donaldsonlab/PPT-Chamber/Main/Dividers/Climbing Wall Drawings/Two_Thirds_climbing_ladder.DXF

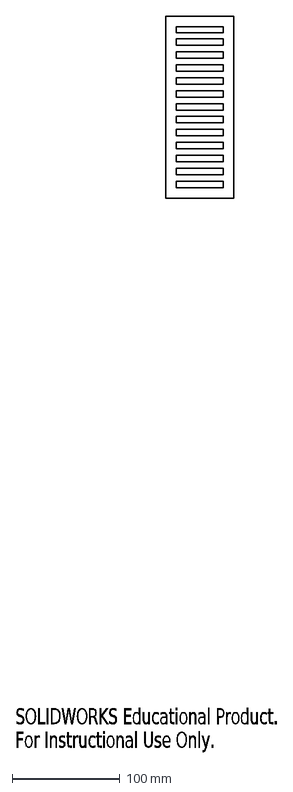
[picture p16: CAD file, 2024-10-31]
Main/Dividers/Climbing Wall Drawings/Two_Thirds_climbing_ladder.DXF
SOLIDWORKS Educational Product.
For Instructional Use Only.
