donaldsonlab/PPT-Chamber/Main/PPT_SideWall.SLDPRT

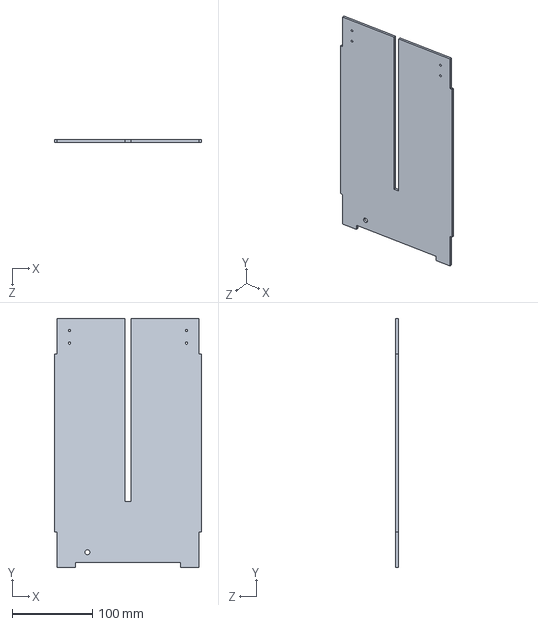
[picture p17: CAD file, 2024-09-06]
Main/PPT_SideWall.SLDPRT
184.1 x 311.1 x 3.17 mm
