donaldsonlab/PPT-Chamber/STL/PPT_cornerBrace_oppo.STL

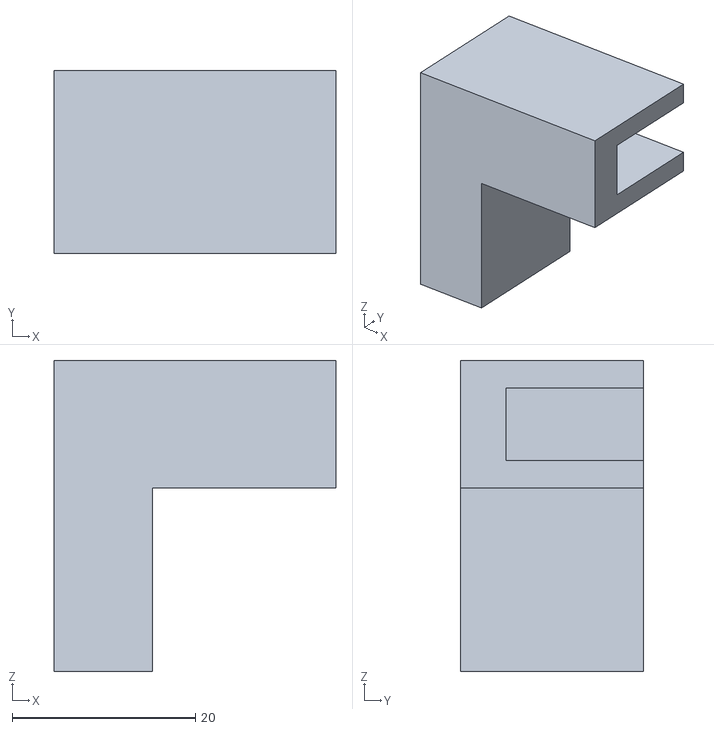
[picture p18: CAD file, 2022-10-21]
STL/PPT_cornerBrace_oppo.STL
30.8 x 20.0 x 33.9
