donaldsonlab/PPT-Chamber/2-Chamber/PPT2_Base.SLDPRT

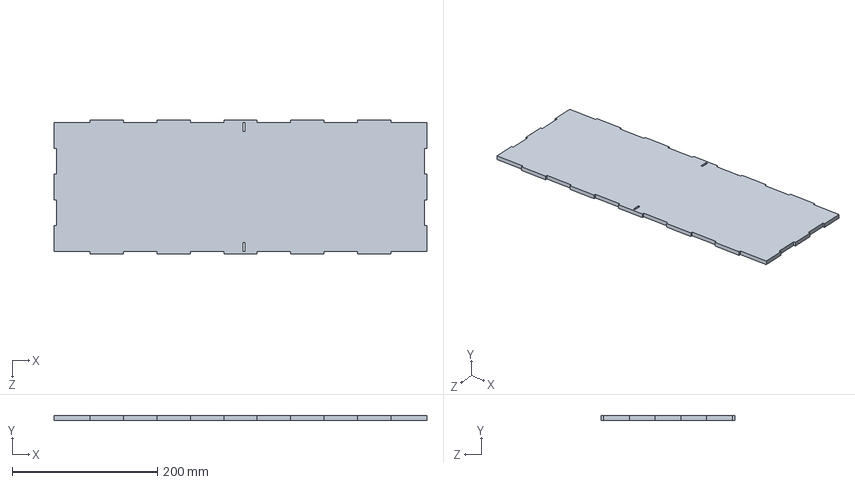
[picture p19: CAD file, 2023-02-03]
2-Chamber/PPT2_Base.SLDPRT
514.3 x 6.35 x 184.2 mm
