donaldsonlab/PPT-Chamber/2-Chamber/printing/slot_cover.DXF

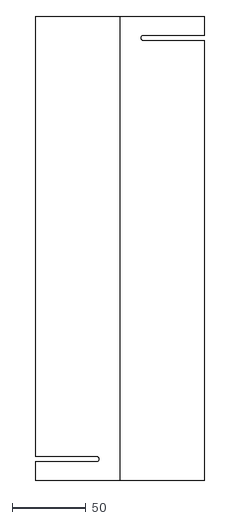
[picture p20: CAD file, 2023-02-03]
2-Chamber/printing/slot_cover.DXF
115.3 x 315.0
