donaldsonlab/PPT-Chamber/Laser Cutting/PPT_Insert_cut.DXF

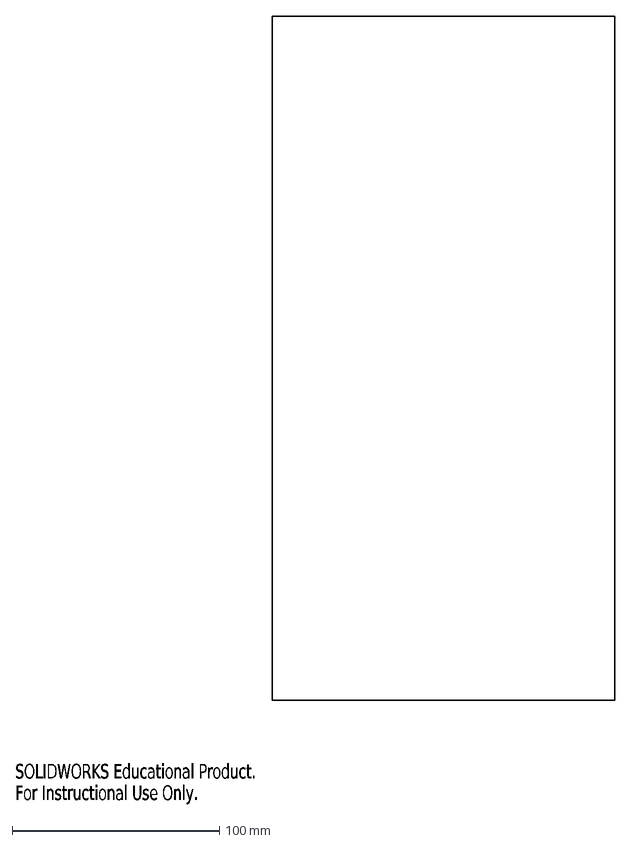
[picture p21: CAD file, 2022-07-01]
Laser Cutting/PPT_Insert_cut.DXF
SOLIDWORKS Educational Product.
For Instructional Use Only.
