donaldsonlab/PPT-Chamber/Main - 2 Chamber PPT/Cutting/PPT_InsertGuide_Large.DXF

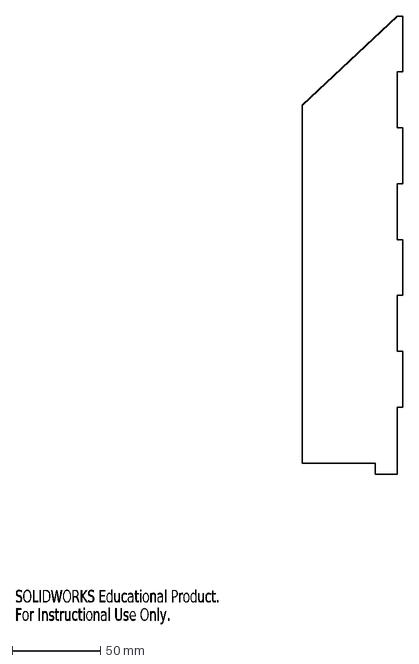
[picture p22: CAD file, 2023-08-11]
Main - 2 Chamber PPT/Cutting/PPT_InsertGuide_Large.DXF
SOLIDWORKS Educational Product.
For Instructional Use Only.
