donaldsonlab/PPT-Chamber/Main - 2 Chamber PPT/drawing files 20231101/PPT_Box_Nest.DXF

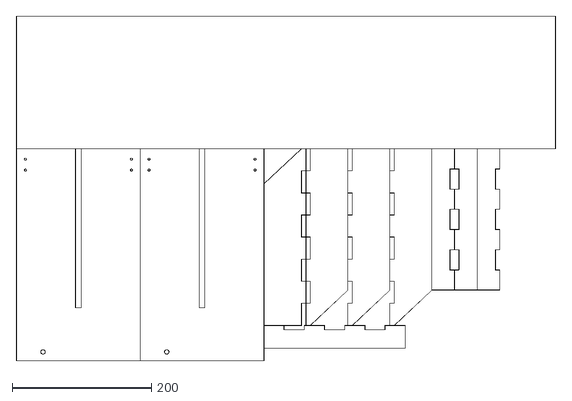
[picture p23: CAD file, 2024-09-06]
Main - 2 Chamber PPT/drawing files 20231101/PPT_Box_Nest.DXF
775.1 x 495.7
