donaldsonlab/PPT-Chamber/Main - 2 Chamber PPT/Drawings/PPT_InsertGuide_Small_longer.DXF

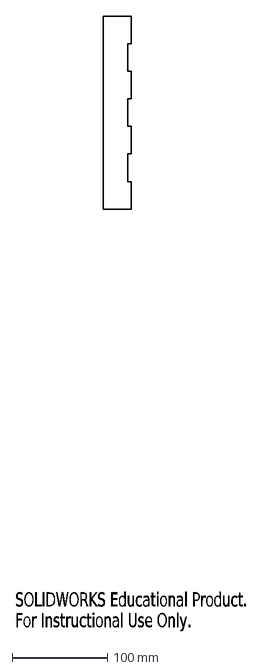
[picture p24: CAD file, 2023-08-11]
Main - 2 Chamber PPT/Drawings/PPT_InsertGuide_Small_longer.DXF
SOLIDWORKS Educational Product.
For Instructional Use Only.
