donaldsonlab/PPT-Chamber/Main/Dividers/perforated_divider.SLDPRT

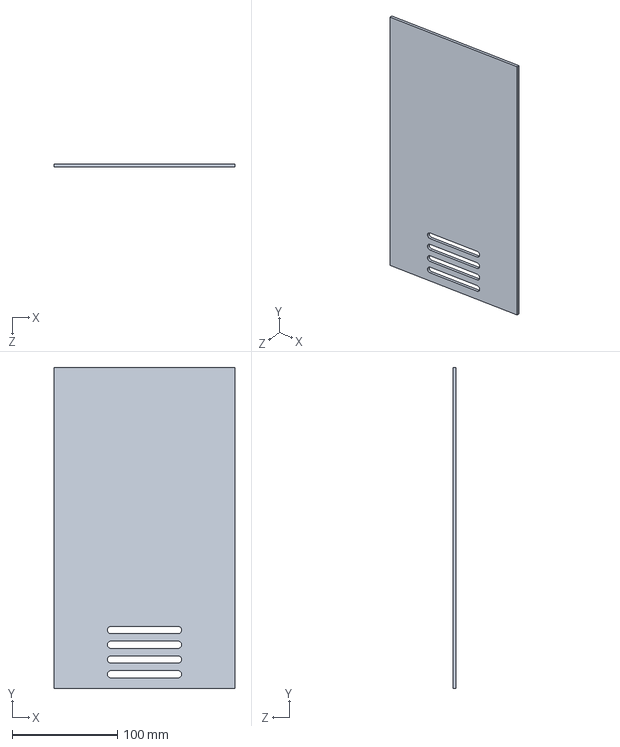
[picture p25: CAD file, 2024-10-31]
Main/Dividers/perforated_divider.SLDPRT
171.4 x 304.8 x 3.17 mm
