donaldsonlab/PPT-Chamber/Main/PPT_LongWall.SLDPRT

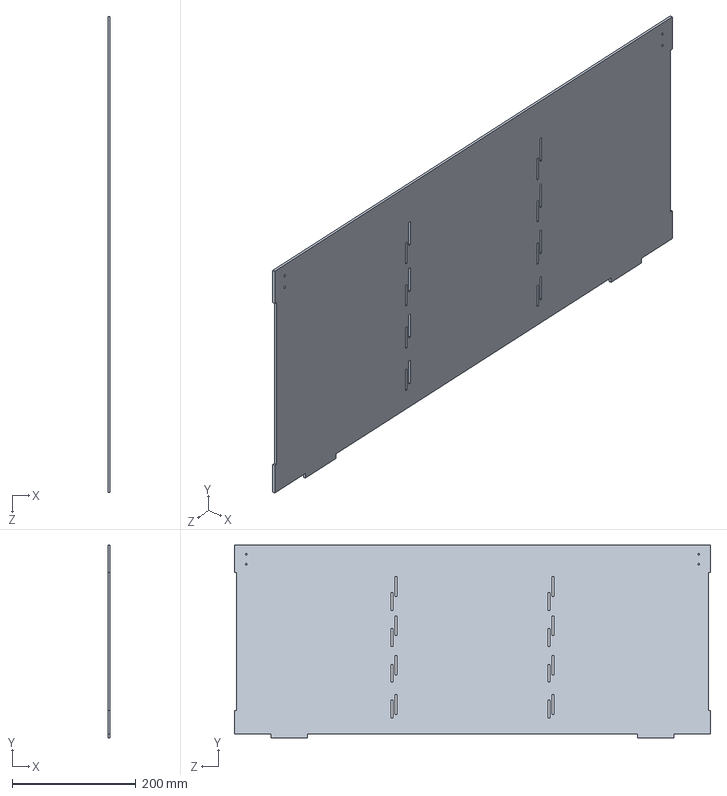
[picture p26: CAD file, 2024-09-06]
Main/PPT_LongWall.SLDPRT
3.17 x 311.1 x 768.3 mm
