donaldsonlab/PPT-Chamber/2-Chamber/PPT2_holeCover.SLDPRT

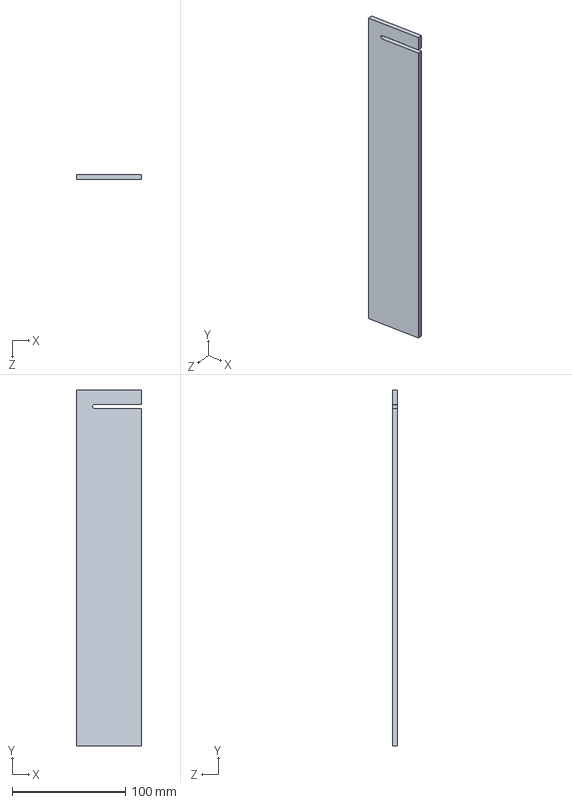
[picture p27: CAD file, 2023-02-03]
2-Chamber/PPT2_holeCover.SLDPRT
57.5 x 314.7 x 4.76 mm
