donaldsonlab/PPT-Chamber/2-Chamber/printing/eigth_inch.DXF

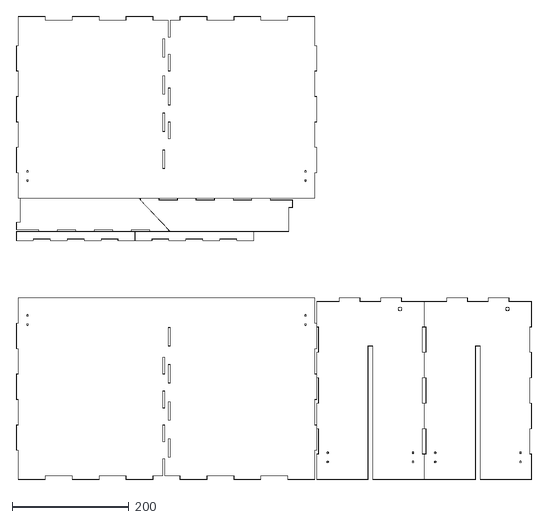
[picture p28: CAD file, 2023-02-03]
2-Chamber/printing/eigth_inch.DXF
883.0 x 793.5
