donaldsonlab/PPT-Chamber/Laser Cutting/PPT_holeCover.DXF

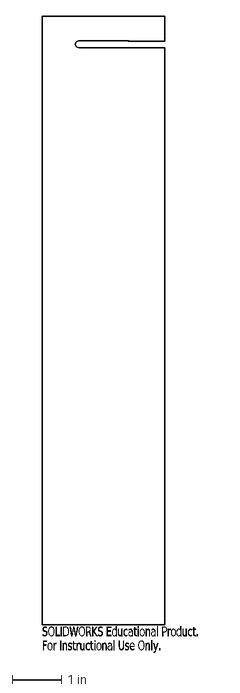
[picture p29: CAD file, 2022-02-18]
Laser Cutting/PPT_holeCover.DXF
SOLIDWORKS Educational Product.
For Instructional Use Only.
