donaldsonlab/PPT-Chamber/Main - 2 Chamber PPT/Cutting/PPT_Insert.DXF

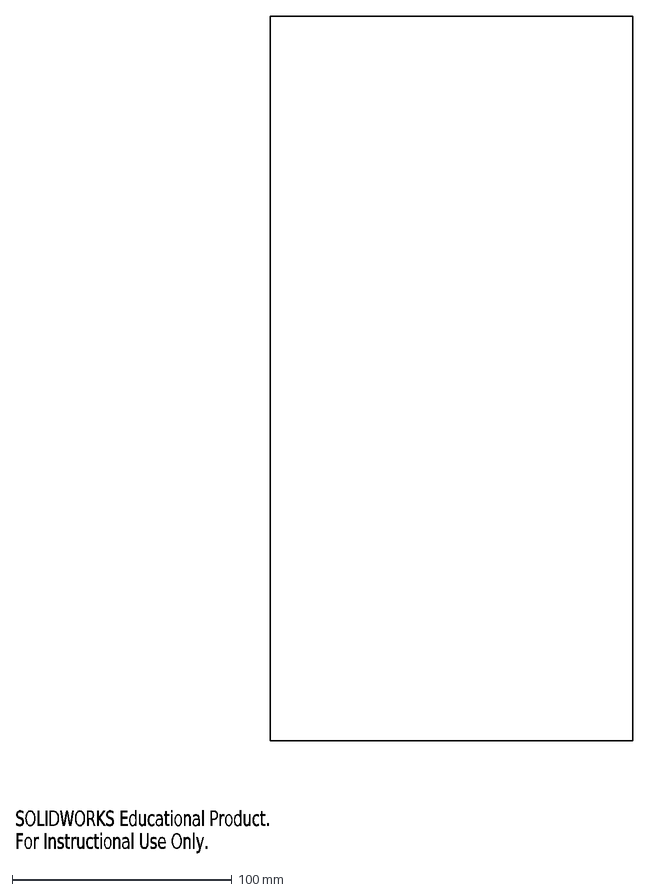
[picture p30: CAD file, 2023-08-11]
Main - 2 Chamber PPT/Cutting/PPT_Insert.DXF
SOLIDWORKS Educational Product.
For Instructional Use Only.
