donaldsonlab/PPT-Chamber/Main - 2 Chamber PPT/drawing files 20231101/PPT_SideWall.DXF

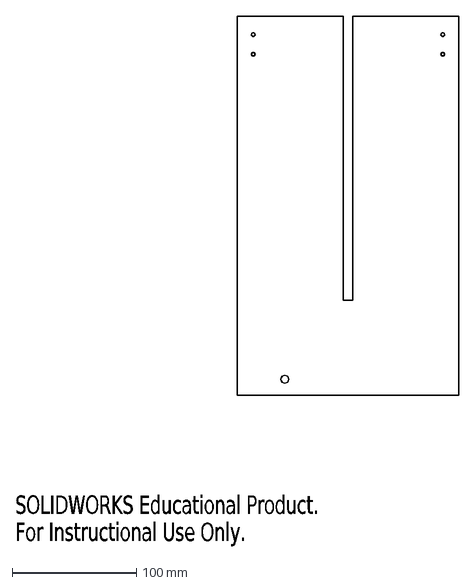
[picture p31: CAD file, 2024-09-06]
Main - 2 Chamber PPT/drawing files 20231101/PPT_SideWall.DXF
SOLIDWORKS Educational Product.
For Instructional Use Only.
