donaldsonlab/PPT-Chamber/Main/Dividers/Climbing Wall Drawings/One_Third_climbing_spacer.DXF

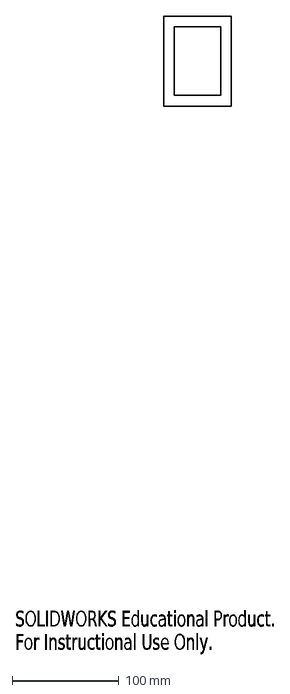
[picture p32: CAD file, 2024-10-31]
Main/Dividers/Climbing Wall Drawings/One_Third_climbing_spacer.DXF
SOLIDWORKS Educational Product.
For Instructional Use Only.
