donaldsonlab/PPT-Chamber/STL/PPT_cornerBracket.STL

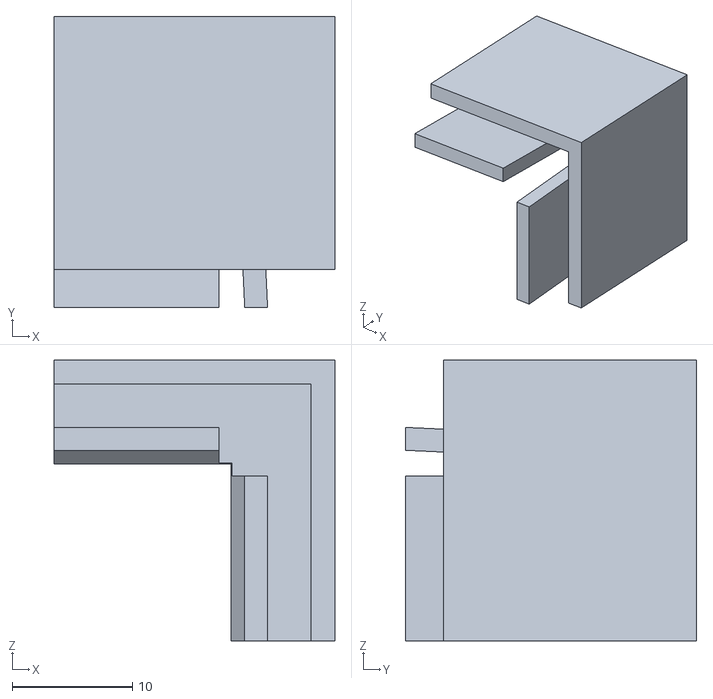
[picture p33: CAD file, 2022-02-18]
STL/PPT_cornerBracket.STL
23.4 x 24.2 x 23.4
