donaldsonlab/PPT-Chamber/Laser Cutting/lasercut1.dxf

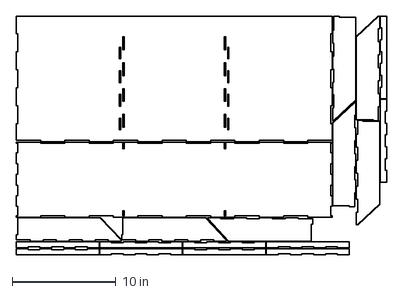
[picture p34: CAD file, 2022-02-18]
Laser Cutting/lasercut1.dxf
35.8 x 23.1 in
