donaldsonlab/PPT-Chamber/Main - 2 Chamber PPT/Cutting/PPT_Floor.DXF

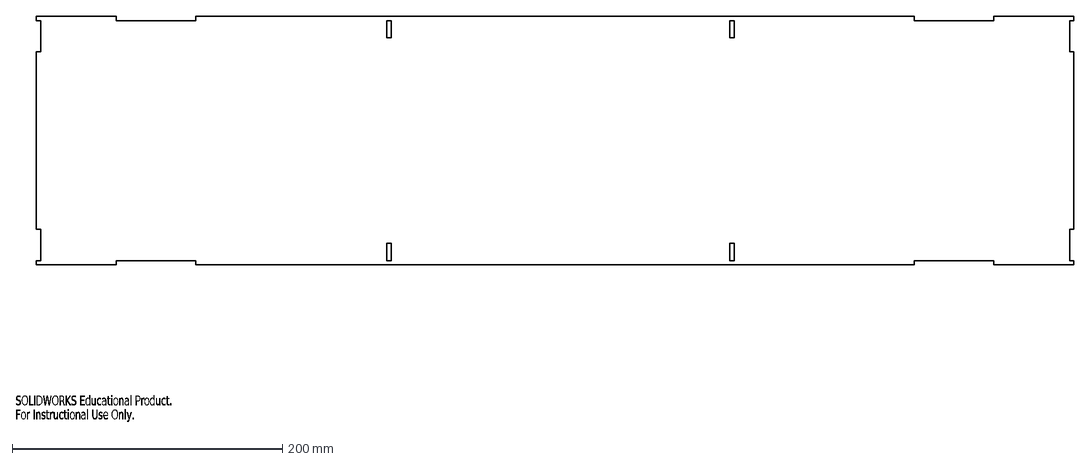
[picture p35: CAD file, 2023-08-11]
Main - 2 Chamber PPT/Cutting/PPT_Floor.DXF
SOLIDWORKS Educational Product.
For Instructional Use Only.
