donaldsonlab/PPT-Chamber/Main - 2 Chamber PPT/drawing files 20231101/PPT_InsertGuide_Large.DXF

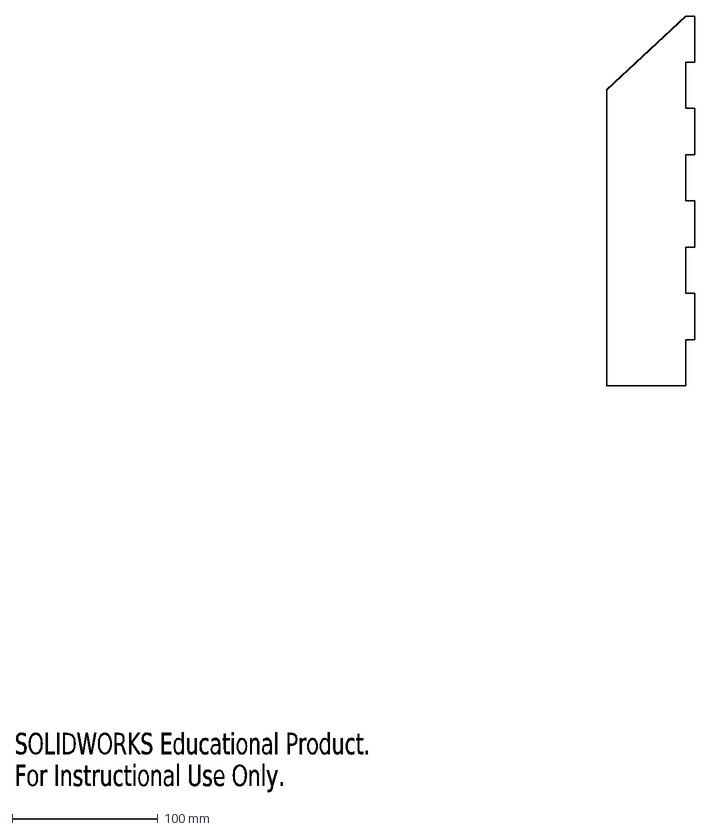
[picture p36: CAD file, 2024-09-06]
Main - 2 Chamber PPT/drawing files 20231101/PPT_InsertGuide_Large.DXF
SOLIDWORKS Educational Product.
For Instructional Use Only.
