donaldsonlab/PPT-Chamber/Main - 2 Chamber PPT/DXF Files 20231108/PPT_SideWall.DXF

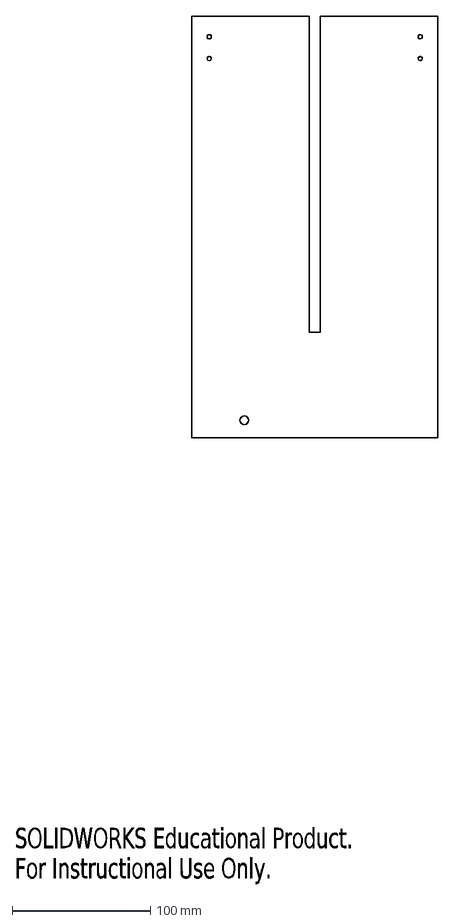
[picture p37: CAD file, 2024-09-06]
Main - 2 Chamber PPT/DXF Files 20231108/PPT_SideWall.DXF
SOLIDWORKS Educational Product.
For Instructional Use Only.
