donaldsonlab/PPT-Chamber/Main - 2 Chamber PPT/PPT_InsertGuide_Large.SLDPRT

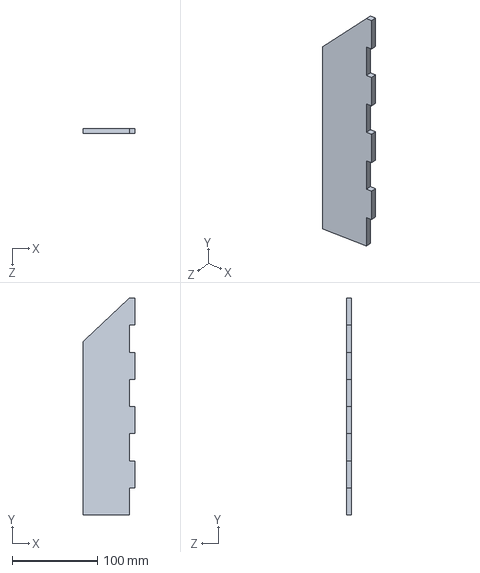
[picture p38: CAD file, 2024-09-06]
Main - 2 Chamber PPT/PPT_InsertGuide_Large.SLDPRT
60.3 x 254.0 x 6.35 mm
