donaldsonlab/PPT-Chamber/Main/Dividers/mesh_divider.SLDPRT

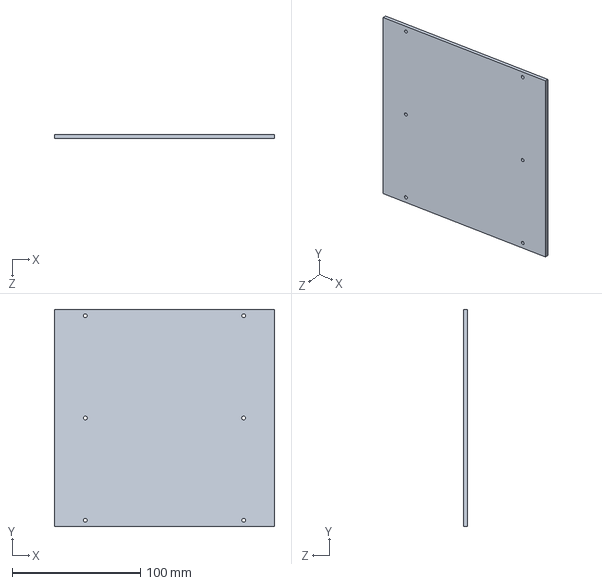
[picture p39: CAD file, 2023-08-11]
Main/Dividers/mesh_divider.SLDPRT
171.4 x 169.3 x 3.17 mm
