donaldsonlab/PPT-Chamber/STL/PPT_miscutPlug.STL

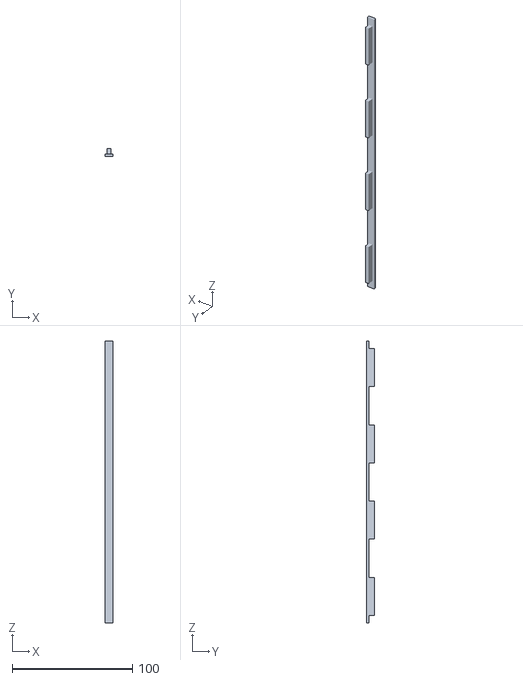
[picture p40: CAD file, 2022-02-18]
STL/PPT_miscutPlug.STL
6.35 x 6.76 x 235.0
