donaldsonlab/PPT-Chamber/2-Chamber/PPT2_Long_Wall.SLDPRT

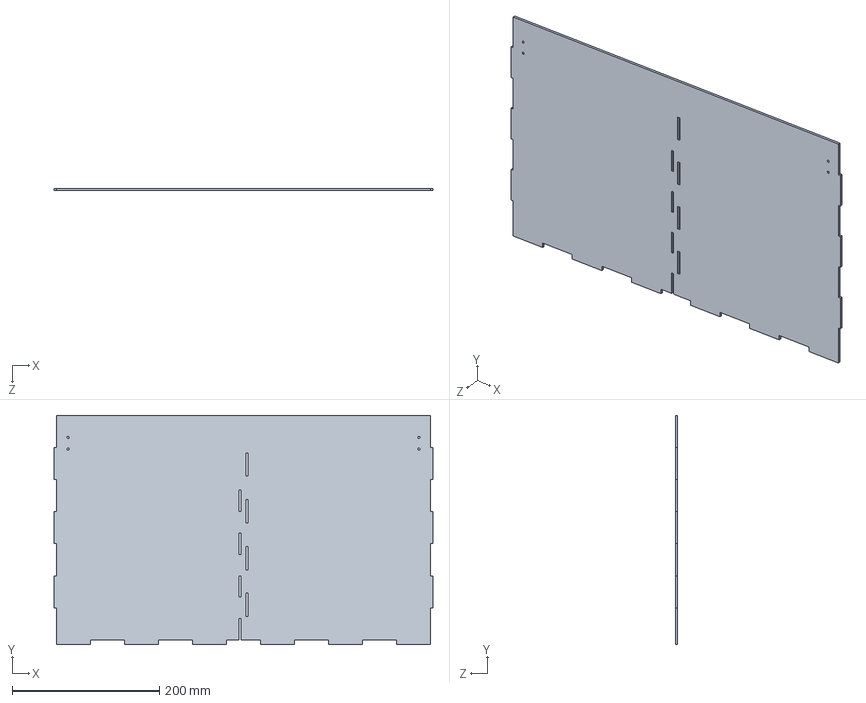
[picture p41: CAD file, 2023-02-03]
2-Chamber/PPT2_Long_Wall.SLDPRT
514.3 x 311.1 x 3.17 mm
