donaldsonlab/PPT-Chamber/Laser Cutting/PPT_Floor.DXF

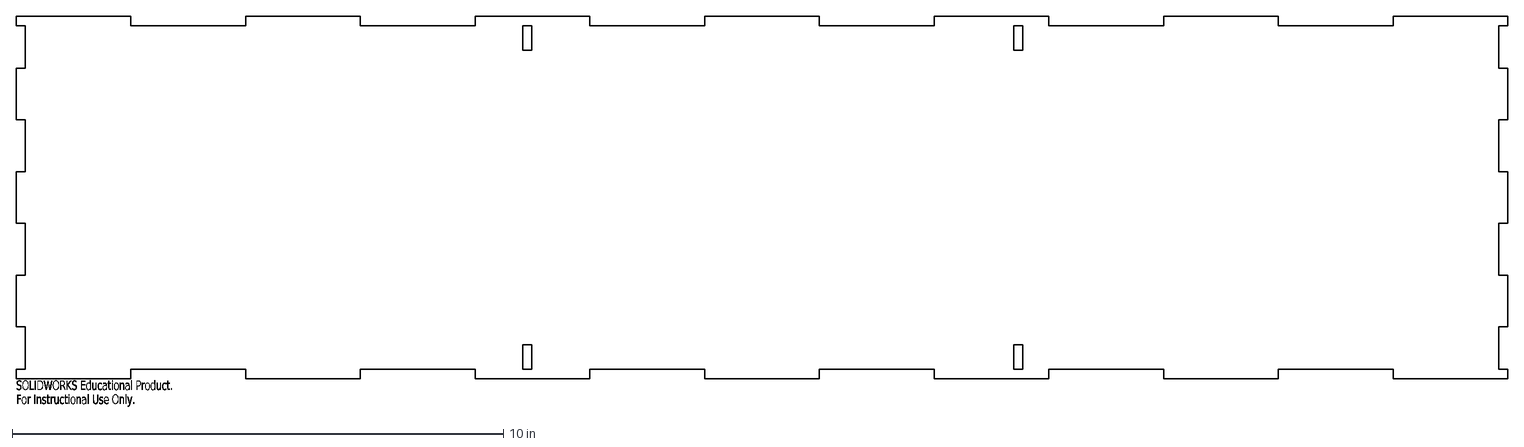
[picture p42: CAD file, 2022-02-18]
Laser Cutting/PPT_Floor.DXF
SOLIDWORKS Educational Product.
For Instructional Use Only.
