donaldsonlab/PPT-Chamber/Main - 2 Chamber PPT/Cutting/PPT_LongWall.DXF

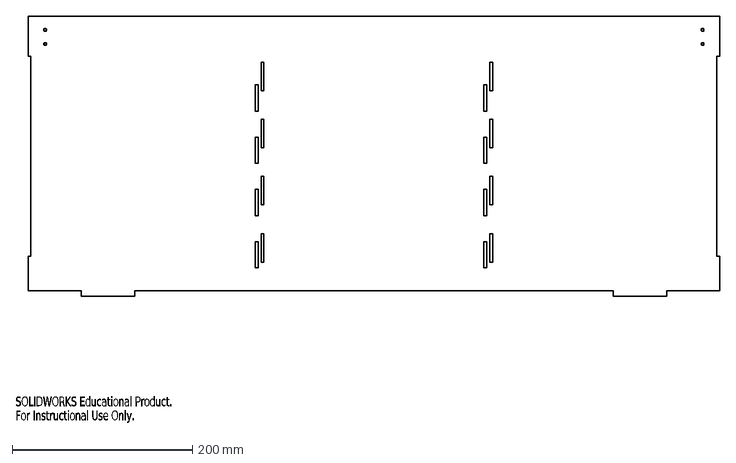
[picture p43: CAD file, 2023-08-11]
Main - 2 Chamber PPT/Cutting/PPT_LongWall.DXF
SOLIDWORKS Educational Product.
For Instructional Use Only.
