donaldsonlab/PPT-Chamber/Main - 2 Chamber PPT/drawing files 20231101/PPT_Floor.DXF

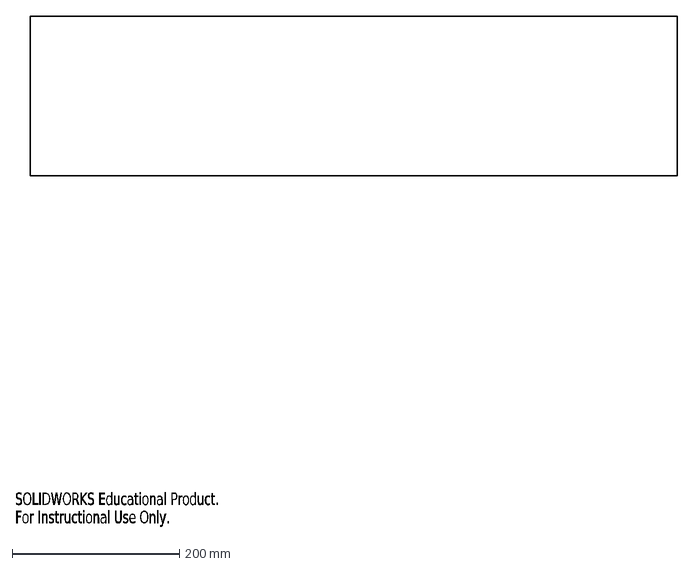
[picture p44: CAD file, 2024-09-06]
Main - 2 Chamber PPT/drawing files 20231101/PPT_Floor.DXF
SOLIDWORKS Educational Product.
For Instructional Use Only.
