donaldsonlab/PPT-Chamber/Main/Dividers/Climbing Wall Drawings/One_Third_climbing_ladder.DXF

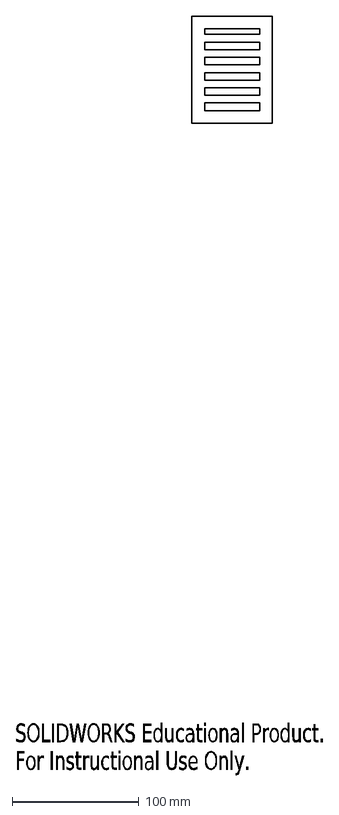
[picture p46: CAD file, 2024-10-31]
Main/Dividers/Climbing Wall Drawings/One_Third_climbing_ladder.DXF
SOLIDWORKS Educational Product.
For Instructional Use Only.
