donaldsonlab/PPT-Chamber/Main/PPT_InsertGuide_Large.SLDPRT

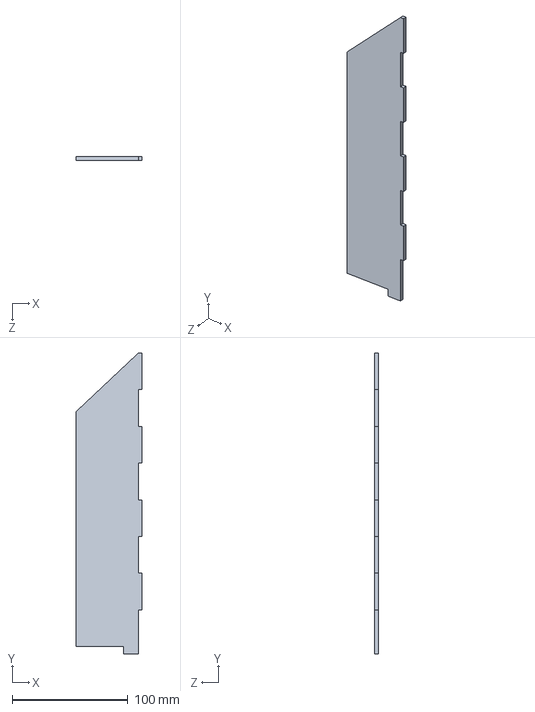
[picture p48: CAD file, 2024-09-06]
Main/PPT_InsertGuide_Large.SLDPRT
57.2 x 260.4 x 3.17 mm
