donaldsonlab/PPT-Chamber/Laser Cutting/PPT_LongWall.DXF

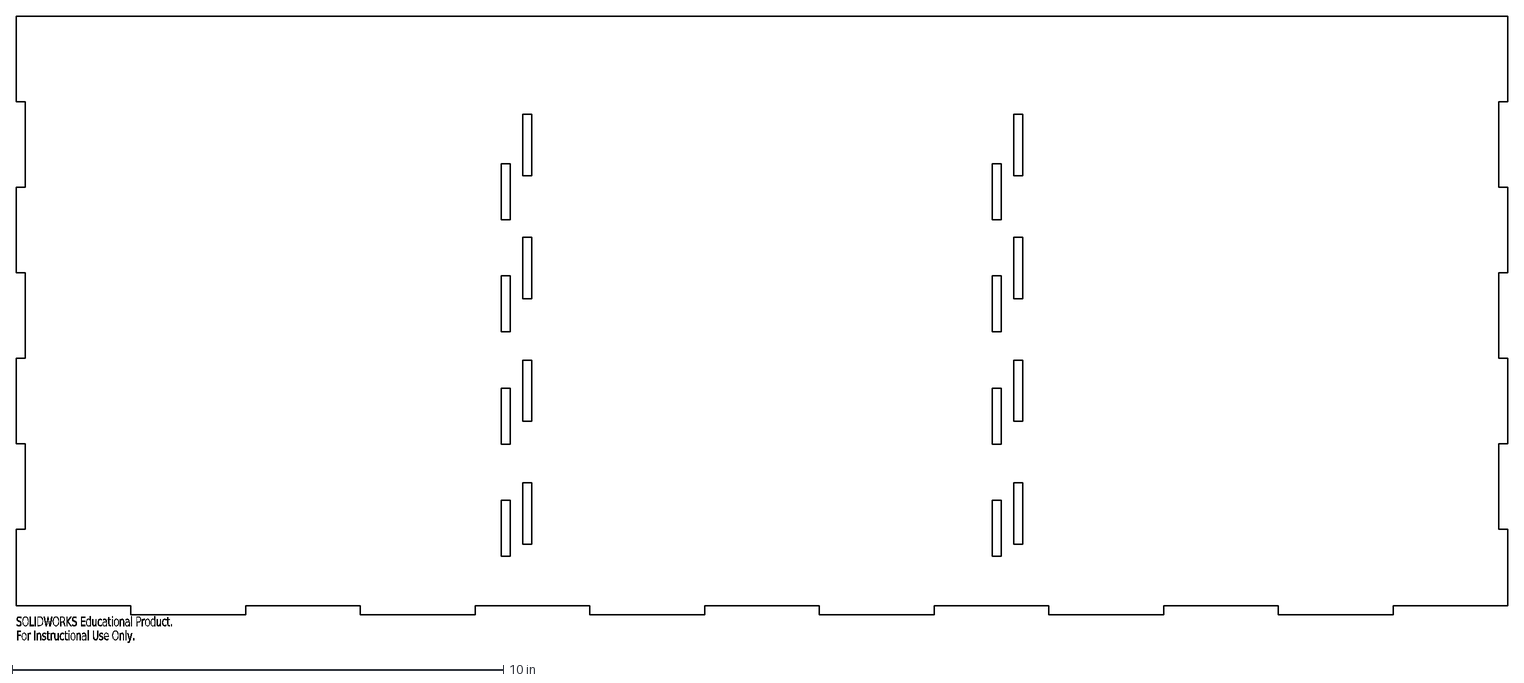
[picture p49: CAD file, 2022-02-18]
Laser Cutting/PPT_LongWall.DXF
SOLIDWORKS Educational Product.
For Instructional Use Only.
