donaldsonlab/PPT-Chamber/Main - 2 Chamber PPT/Cutting/PPT_InsertGuide_Small.DXF

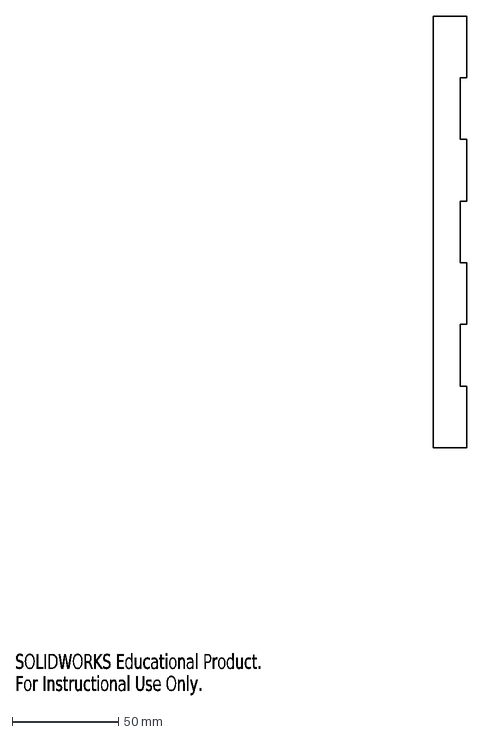
[picture p50: CAD file, 2023-08-11]
Main - 2 Chamber PPT/Cutting/PPT_InsertGuide_Small.DXF
SOLIDWORKS Educational Product.
For Instructional Use Only.
