donaldsonlab/PPT-Chamber/Main - 2 Chamber PPT/drawing files 20231101/PPT_LongWall.DXF

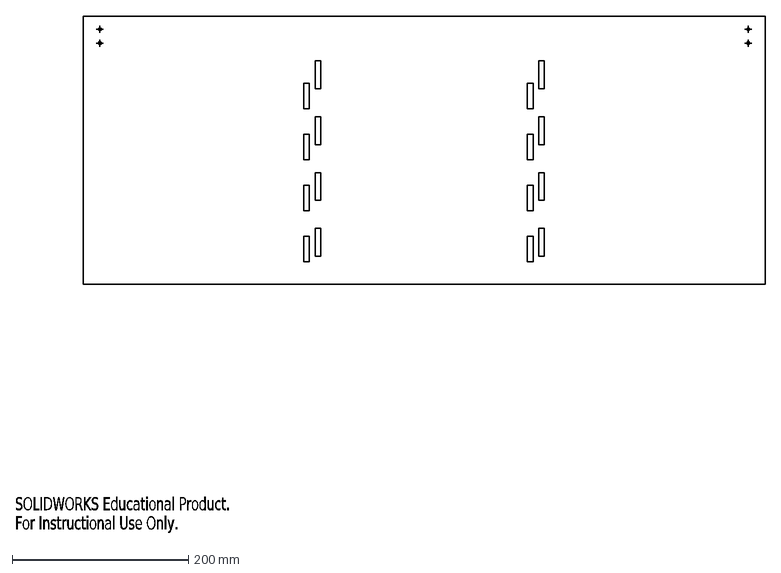
[picture p51: CAD file, 2024-09-06]
Main - 2 Chamber PPT/drawing files 20231101/PPT_LongWall.DXF
SOLIDWORKS Educational Product.
For Instructional Use Only.
