donaldsonlab/PPT-Chamber/Main - 2 Chamber PPT/DXF Files 20231108/PPT_LongWall.DXF

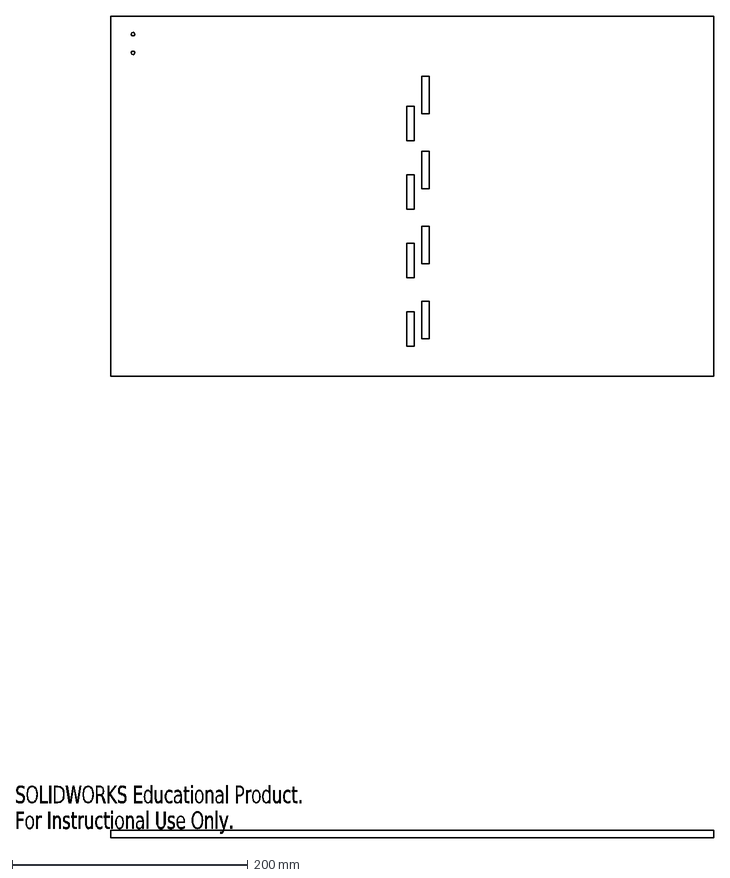
[picture p52: CAD file, 2024-09-06]
Main - 2 Chamber PPT/DXF Files 20231108/PPT_LongWall.DXF
SOLIDWORKS Educational Product.
For Instructional Use Only.
