donaldsonlab/PPT-Chamber/Main - 2 Chamber PPT/PPT_Floor.SLDPRT

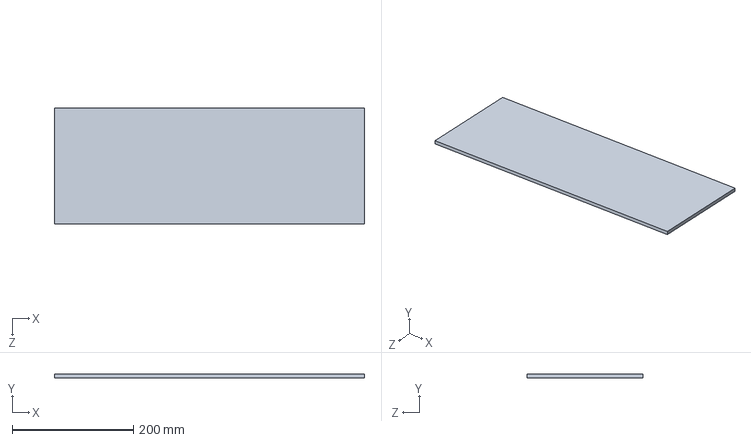
[picture p53: CAD file, 2024-09-06]
Main - 2 Chamber PPT/PPT_Floor.SLDPRT
511.2 x 6.35 x 190.5 mm
