donaldsonlab/PPT-Chamber/Main/Dividers/Climbing Wall Drawings/Two Thirds climbing_spacer.DXF

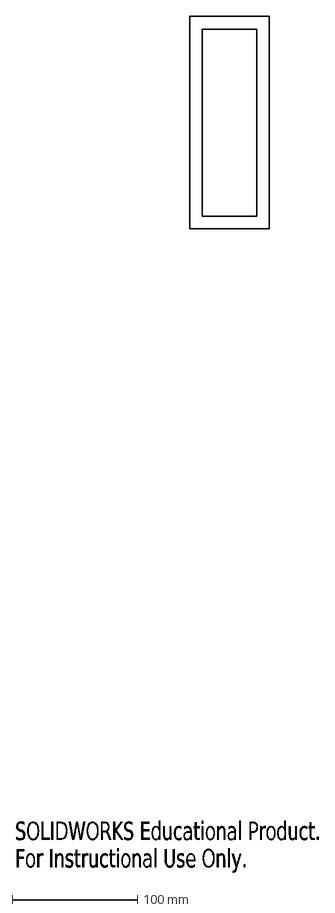
[picture p54: CAD file, 2024-10-31]
Main/Dividers/Climbing Wall Drawings/Two Thirds climbing_spacer.DXF
SOLIDWORKS Educational Product.
For Instructional Use Only.
