donaldsonlab/PPT-Chamber/Main/PPT_Floor.SLDPRT

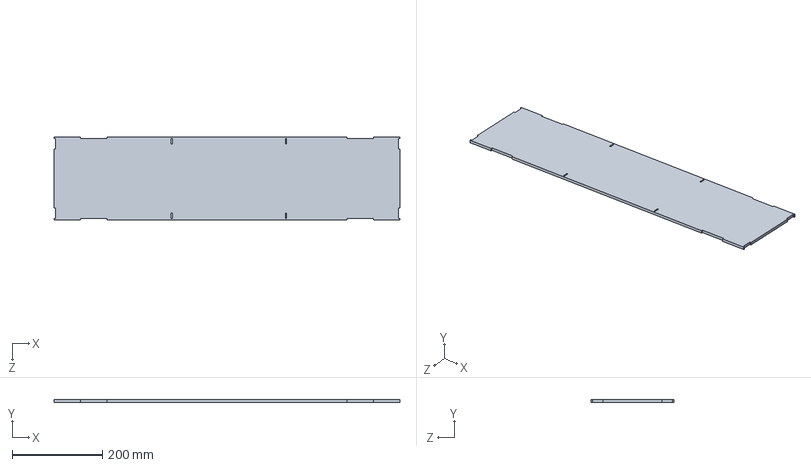
[picture p55: CAD file, 2024-09-06]
Main/PPT_Floor.SLDPRT
768.3 x 6.35 x 184.1 mm
