donaldsonlab/PPT-Chamber/2-Chamber/PPT2_InsertGuide_Small.SLDPRT

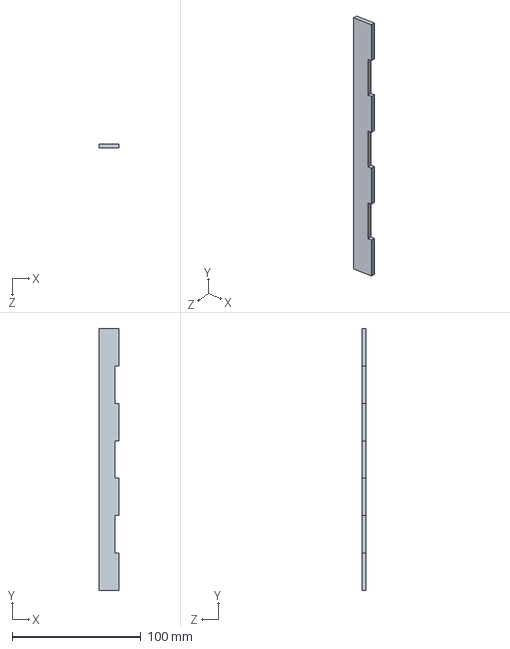
[picture p56: CAD file, 2023-02-03]
2-Chamber/PPT2_InsertGuide_Small.SLDPRT
15.9 x 203.2 x 3.17 mm
