donaldsonlab/PPT-Chamber/Laser Cutting/PPT_SideWall.DXF

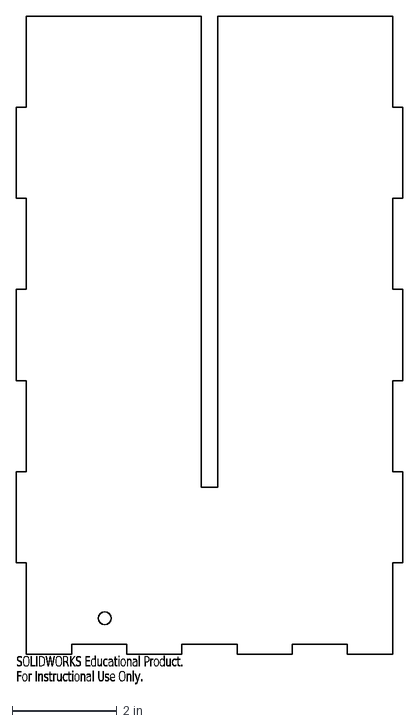
[picture p57: CAD file, 2022-02-18]
Laser Cutting/PPT_SideWall.DXF
SOLIDWORKS Educational Product.
For Instructional Use Only.
