donaldsonlab/PPT-Chamber/Main - 2 Chamber PPT/Cutting/inserts.DXF

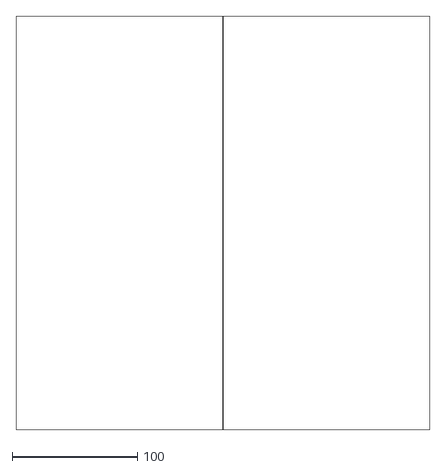
[picture p58: CAD file, 2023-05-15]
Main - 2 Chamber PPT/Cutting/inserts.DXF
330.6 x 330.6
