donaldsonlab/PPT-Chamber/Main - 2 Chamber PPT/PPT_SideWall.SLDPRT

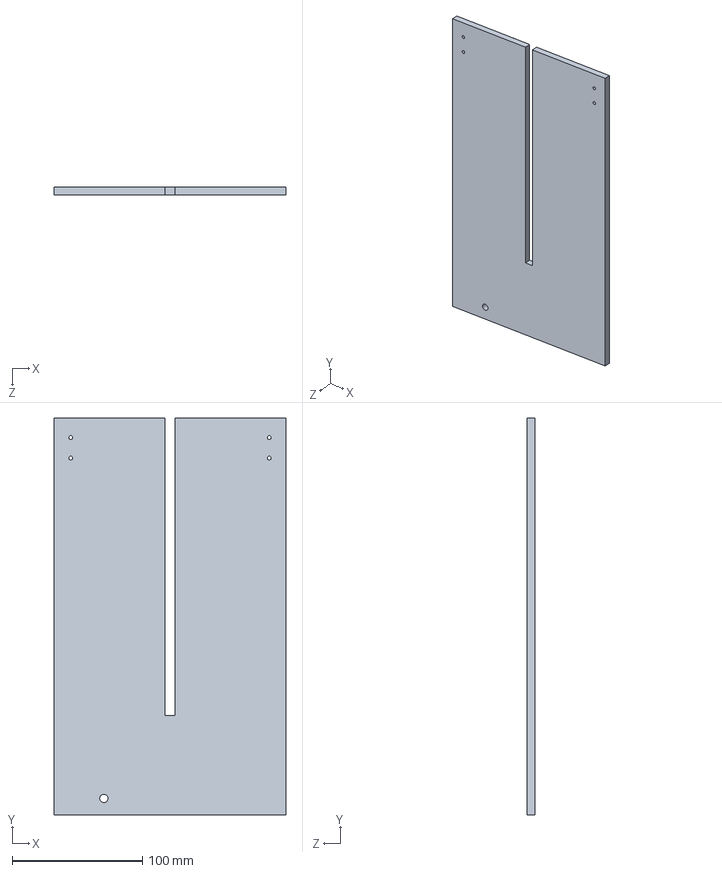
[picture p59: CAD file, 2024-09-06]
Main - 2 Chamber PPT/PPT_SideWall.SLDPRT
177.8 x 304.8 x 6.35 mm
