donaldsonlab/PPT-Chamber/Main/Dividers/mesh_divider_1-3Default.DXF

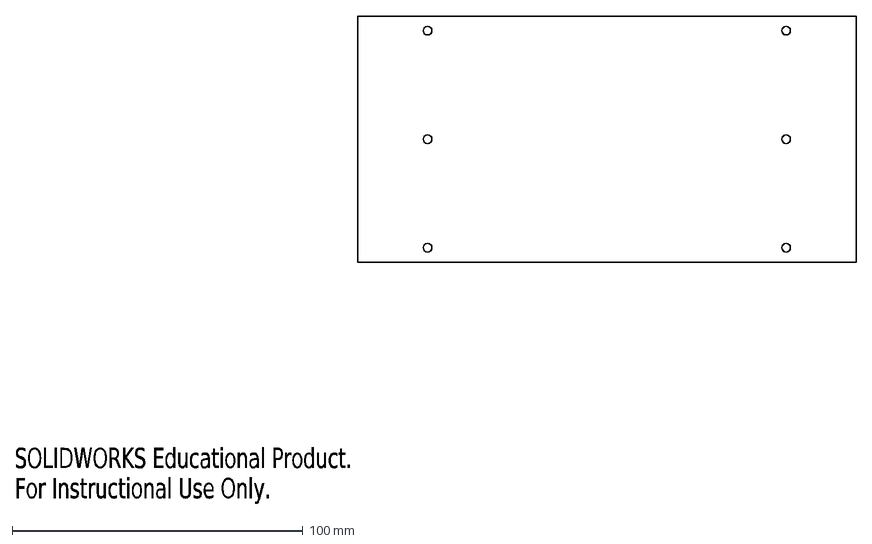
[picture p60: CAD file, 2023-08-11]
Main/Dividers/mesh_divider_1-3Default.DXF
SOLIDWORKS Educational Product.
For Instructional Use Only.
