donaldsonlab/PPT-Chamber/Laser Cutting/PPT_MiddleStrip.DXF

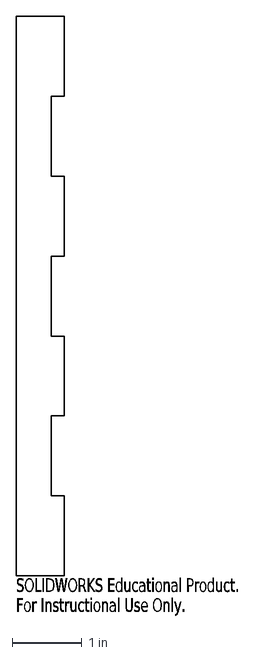
[picture p61: CAD file, 2022-02-18]
Laser Cutting/PPT_MiddleStrip.DXF
SOLIDWORKS Educational Product.
For Instructional Use Only.
