donaldsonlab/PPT-Chamber/Main - 2 Chamber PPT/Cutting/end_walls.DXF

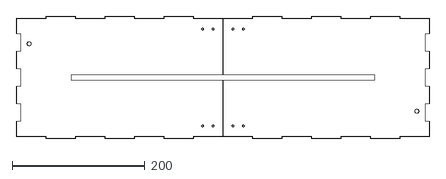
[picture p62: CAD file, 2023-02-03]
Main - 2 Chamber PPT/Cutting/end_walls.DXF
622.7 x 184.5
