donaldsonlab/PPT-Chamber/Main/Dividers/Climbing Wall Drawings/mesh_divider_2-3Default.DXF

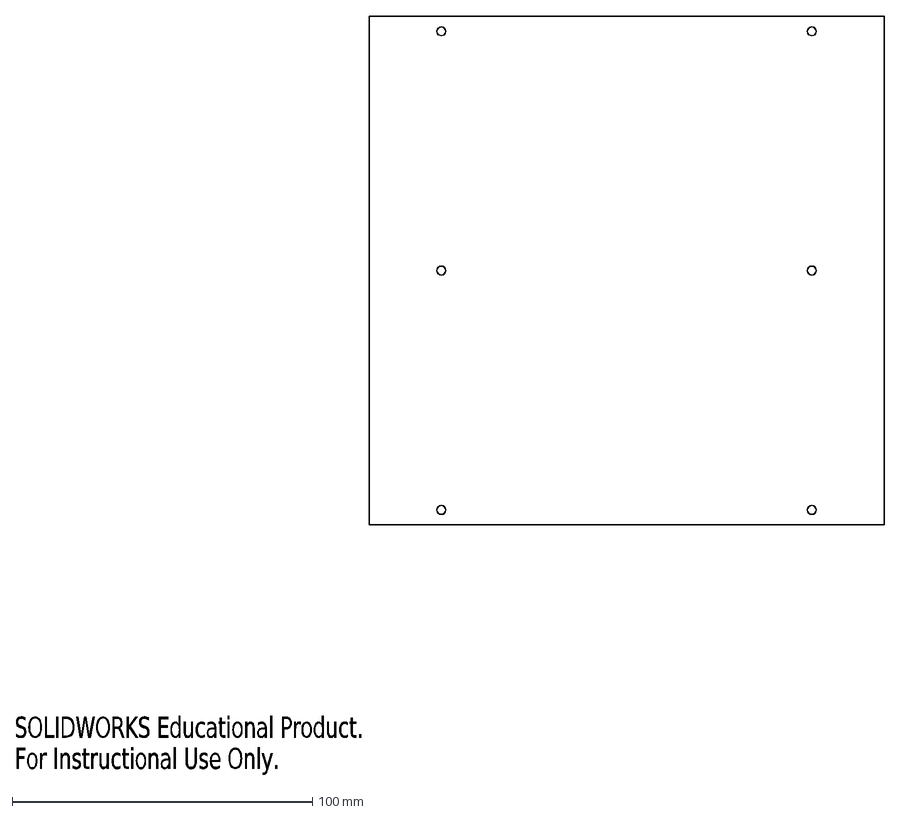
[picture p63: CAD file, 2023-08-11]
Main/Dividers/Climbing Wall Drawings/mesh_divider_2-3Default.DXF
SOLIDWORKS Educational Product.
For Instructional Use Only.
