donaldsonlab/PPT-Chamber/2-Chamber/wall_bracket.SLDPRT

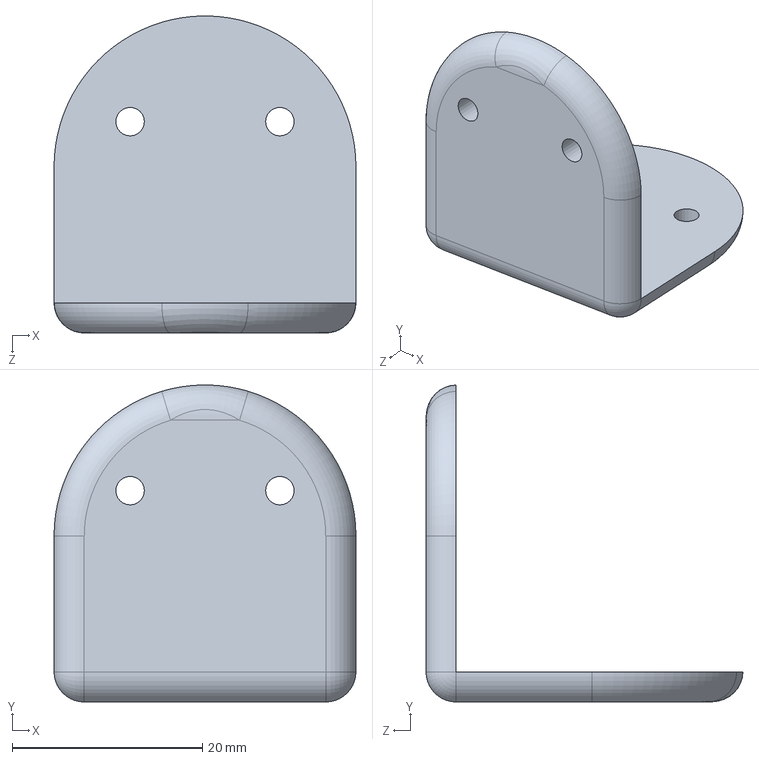
[picture p64: CAD file, 2022-11-23]
2-Chamber/wall_bracket.SLDPRT
31.8 x 33.3 x 33.3 mm
