donaldsonlab/PPT-Chamber/Laser Cutting/lasercut5.dxf

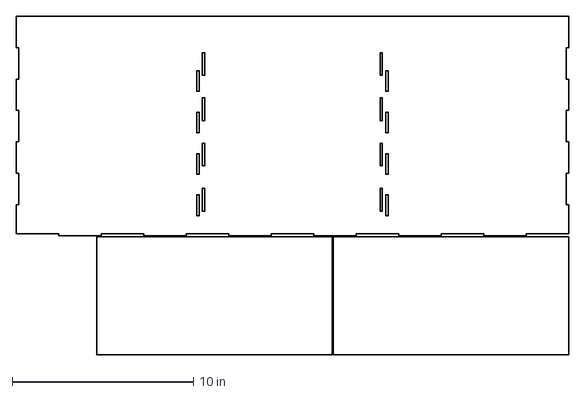
[picture p65: CAD file, 2022-02-18]
Laser Cutting/lasercut5.dxf
30.5 x 18.7 in
