donaldsonlab/PPT-Chamber/Main - 2 Chamber PPT/Cutting/PPT_holeCover.DXF

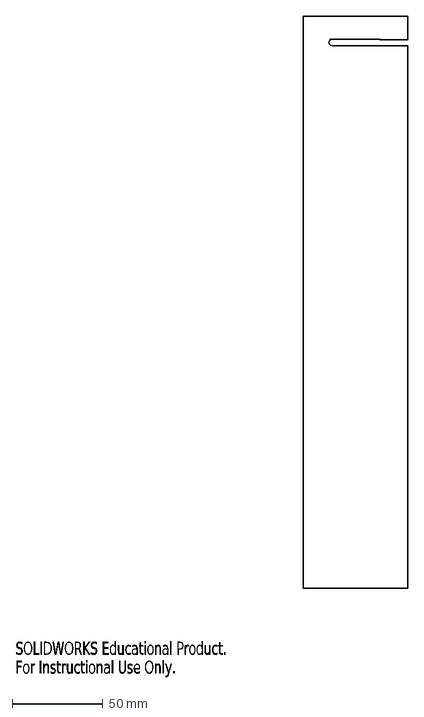
[picture p66: CAD file, 2023-02-03]
Main - 2 Chamber PPT/Cutting/PPT_holeCover.DXF
SOLIDWORKS Educational Product.
For Instructional Use Only.
