donaldsonlab/PPT-Chamber/Main - 2 Chamber PPT/PPT_InsertGuide_Small.SLDPRT

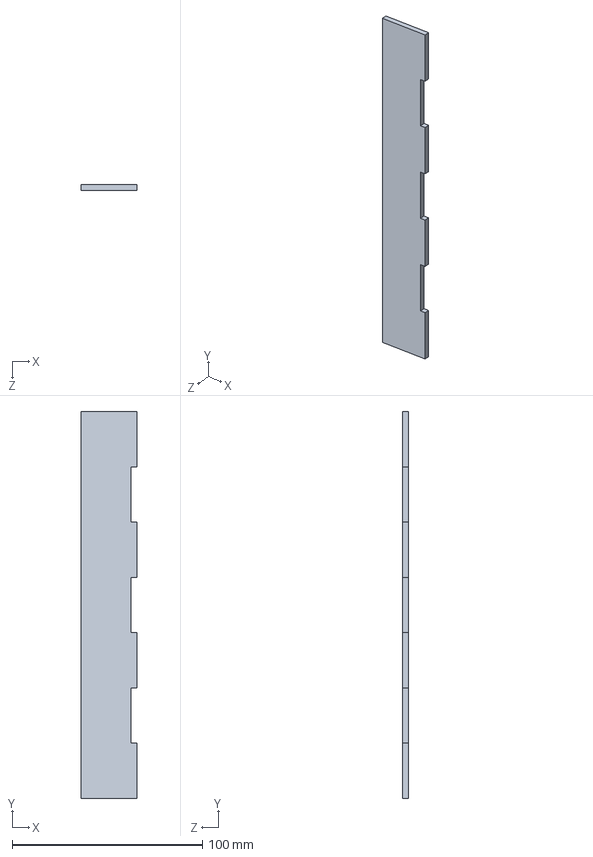
[picture p67: CAD file, 2024-09-06]
Main - 2 Chamber PPT/PPT_InsertGuide_Small.SLDPRT
29.4 x 203.2 x 3.17 mm
