donaldsonlab/PPT-Chamber/2-Chamber/PPT2_Insert.SLDPRT

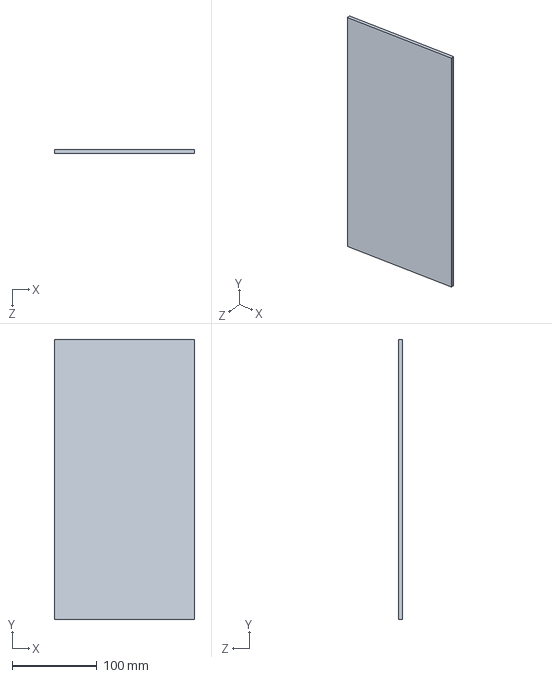
[picture p68: CAD file, 2022-11-11]
2-Chamber/PPT2_Insert.SLDPRT
165.1 x 330.2 x 4.76 mm
