donaldsonlab/PPT-Chamber/Laser Cutting/lasercut6.dxf

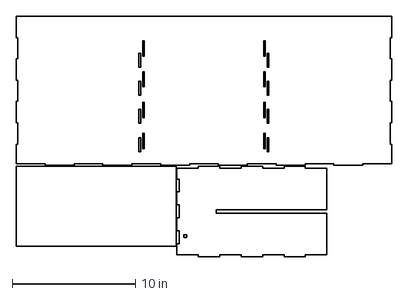
[picture p69: CAD file, 2022-02-18]
Laser Cutting/lasercut6.dxf
30.5 x 19.6 in
