donaldsonlab/PPT-Chamber/Main - 2 Chamber PPT/PPT_Insert.SLDPRT

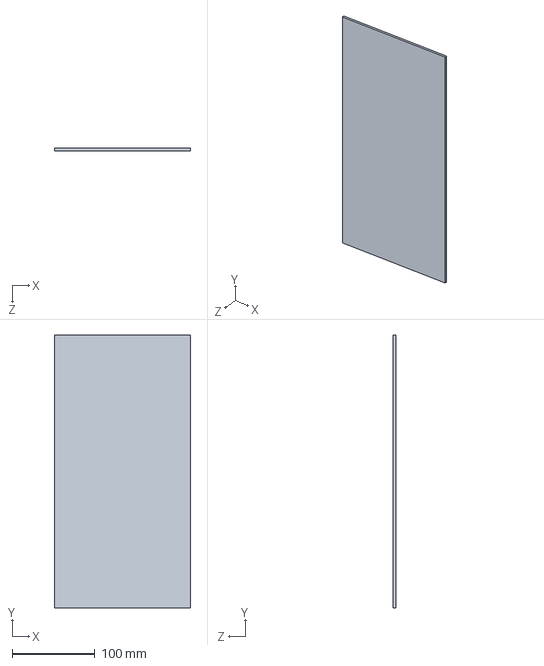
[picture p70: CAD file, 2023-08-11]
Main - 2 Chamber PPT/PPT_Insert.SLDPRT
165.1 x 330.2 x 3.17 mm
