donaldsonlab/PPT-Chamber/Main/Dividers/mesh_divider2-3Cut.DXF

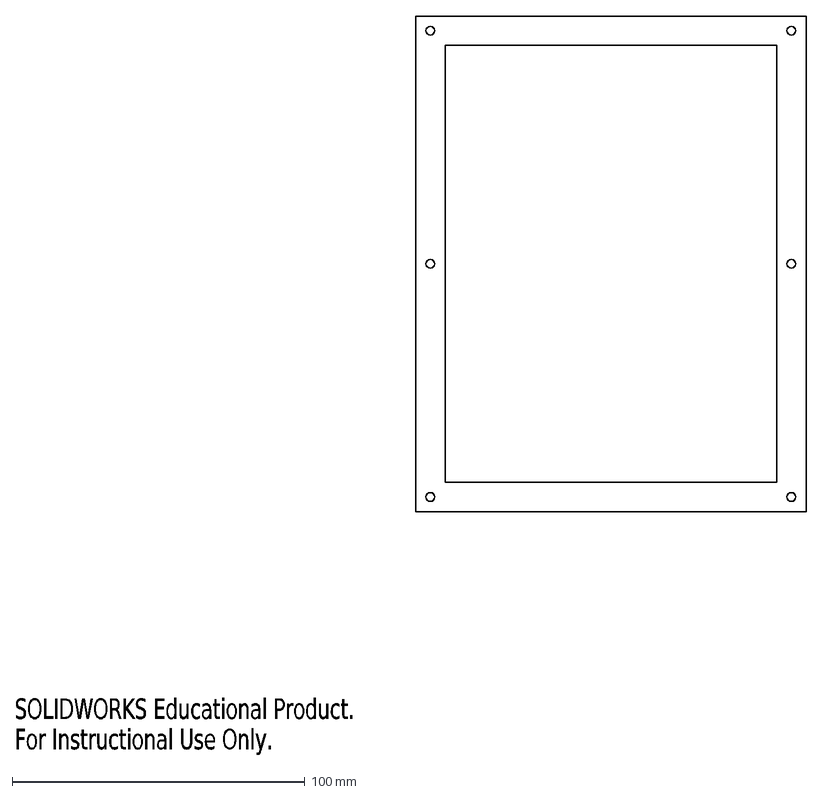
[picture p71: CAD file, 2023-08-11]
Main/Dividers/mesh_divider2-3Cut.DXF
SOLIDWORKS Educational Product.
For Instructional Use Only.
