donaldsonlab/PPT-Chamber/Laser Cutting/lasercut2.dxf

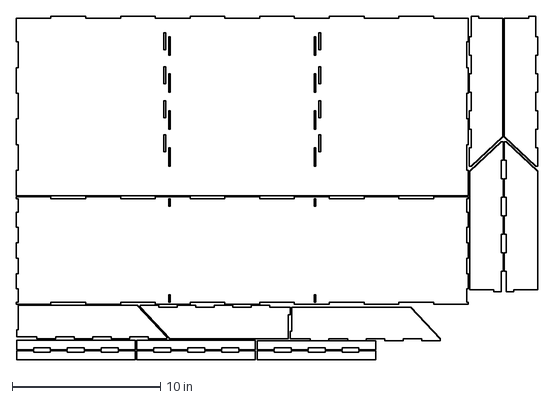
[picture p72: CAD file, 2022-02-18]
Laser Cutting/lasercut2.dxf
35.2 x 23.2 in
