donaldsonlab/PPT-Chamber/Main - 2 Chamber PPT/DXF Files 20231108/PPT_InsertGuide_Large.DXF

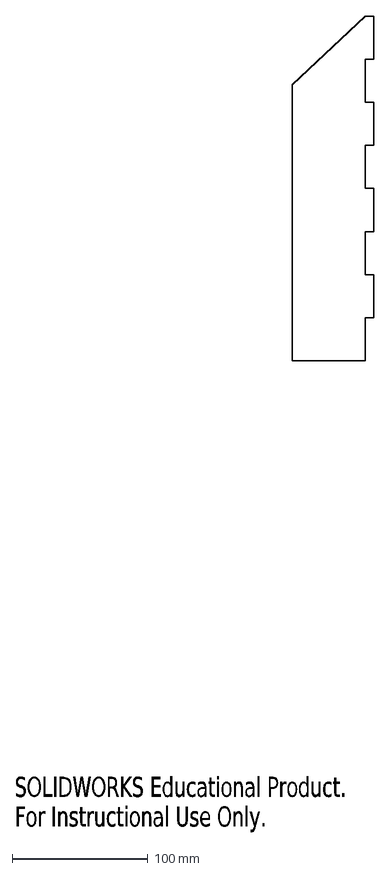
[picture p73: CAD file, 2024-09-06]
Main - 2 Chamber PPT/DXF Files 20231108/PPT_InsertGuide_Large.DXF
SOLIDWORKS Educational Product.
For Instructional Use Only.
