donaldsonlab/PPT-Chamber/Main - 2 Chamber PPT/PPT_MiddleStrip.SLDPRT

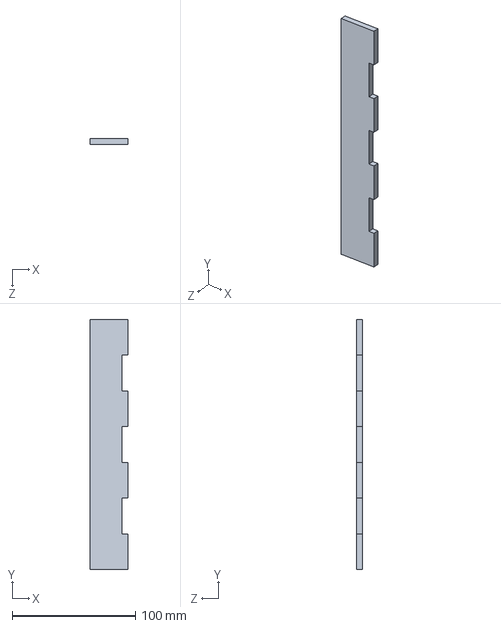
[picture p74: CAD file, 2023-08-11]
Main - 2 Chamber PPT/PPT_MiddleStrip.SLDPRT
31.0 x 203.2 x 4.76 mm
