donaldsonlab/PPT-Chamber/Laser Cutting/lasercut3.dxf

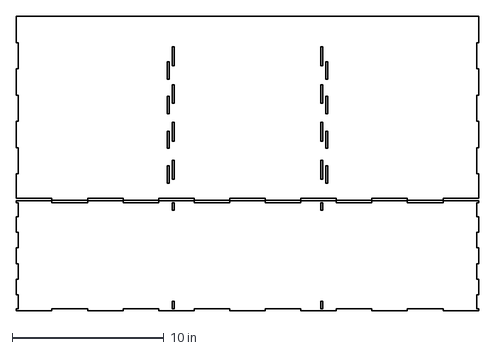
[picture p75: CAD file, 2022-02-18]
Laser Cutting/lasercut3.dxf
30.5 x 19.4 in
