donaldsonlab/PPT-Chamber/Main - 2 Chamber PPT/DXF Files 20231108/PPT_InsertGuide_Small.DXF

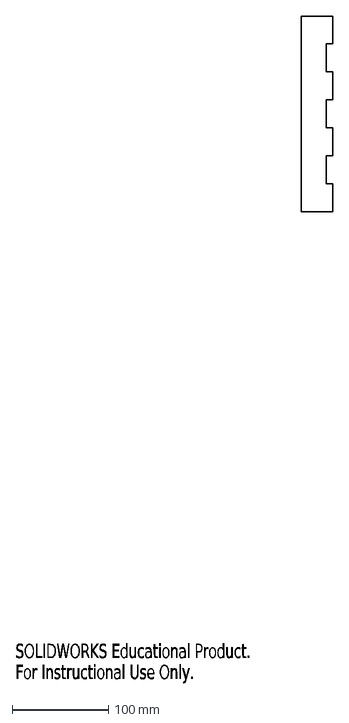
[picture p76: CAD file, 2024-09-06]
Main - 2 Chamber PPT/DXF Files 20231108/PPT_InsertGuide_Small.DXF
SOLIDWORKS Educational Product.
For Instructional Use Only.
