donaldsonlab/PPT-Chamber/Laser Cutting/bounding.SLDPRT

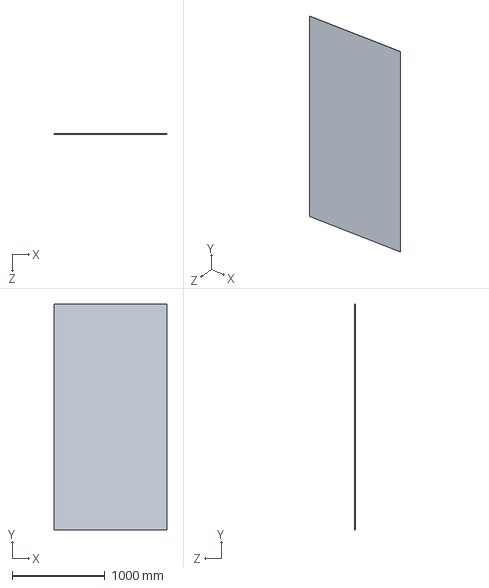
[picture p77: CAD file, 2022-02-18]
Laser Cutting/bounding.SLDPRT
1219.2 x 2438.4 x 3.00 mm
