donaldsonlab/PPT-Chamber/Laser Cutting/lasercut4.dxf

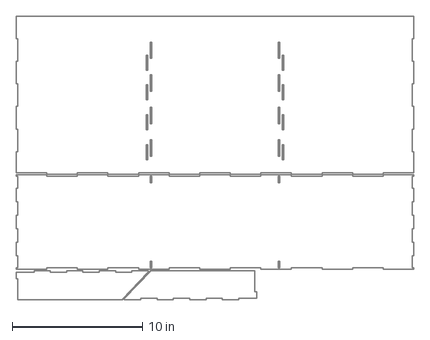
[picture p78: CAD file, 2022-02-18]
Laser Cutting/lasercut4.dxf
30.5 x 21.8 in
