donaldsonlab/PPT-Chamber/Laser Cutting/PPT_Insert.DXF

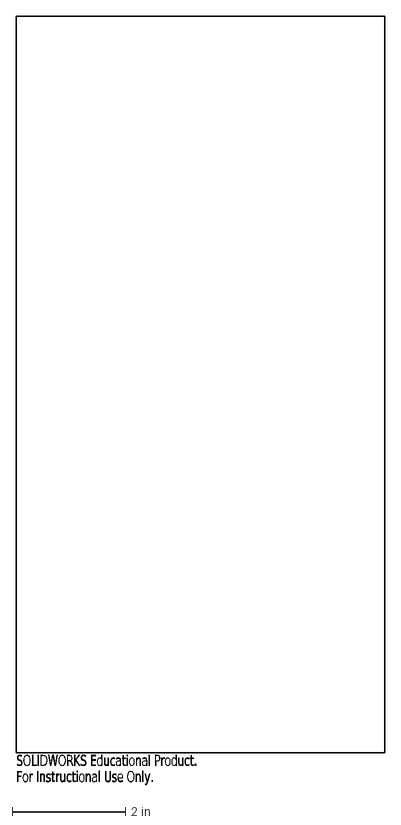
[picture p79: CAD file, 2022-02-18]
Laser Cutting/PPT_Insert.DXF
SOLIDWORKS Educational Product.
For Instructional Use Only.
