donaldsonlab/PPT-Chamber/Laser Cutting/lasercut7_8.dxf

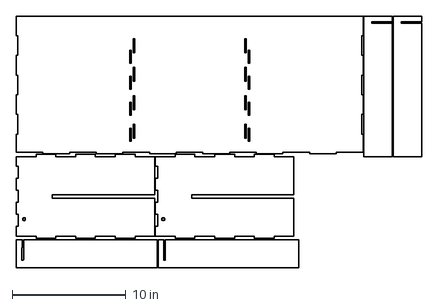
[picture p80: CAD file, 2022-02-18]
Laser Cutting/lasercut7_8.dxf
35.7 x 22.2 in
