donaldsonlab/PPT-Chamber/Laser Cutting/lasercut9.dxf

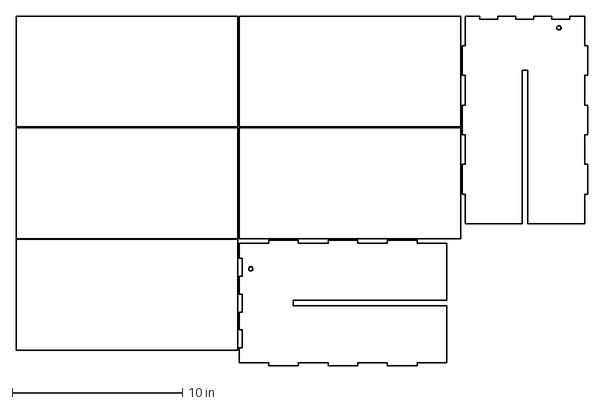
[picture p81: CAD file, 2022-02-18]
Laser Cutting/lasercut9.dxf
33.5 x 20.5 in
