donaldsonlab/PPT-Chamber/Main - 2 Chamber PPT/PPT_SideWall_dark.SLDPRT

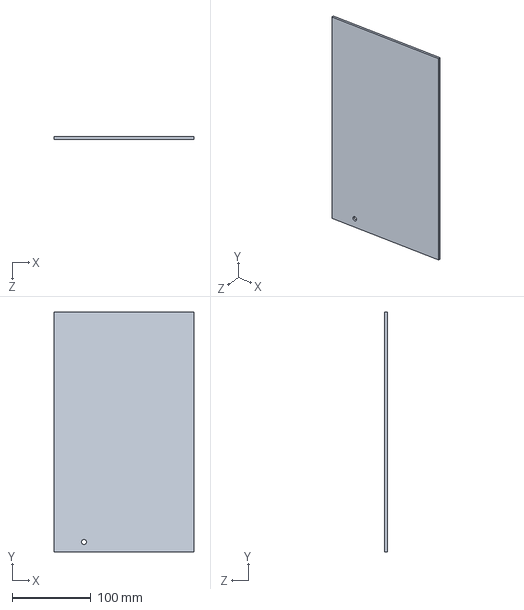
[picture p82: CAD file, 2022-10-21]
Main - 2 Chamber PPT/PPT_SideWall_dark.SLDPRT
177.8 x 304.8 x 3.17 mm
