donaldsonlab/PPT-Chamber/Laser Cutting/PPT_MiddleWall.DXF

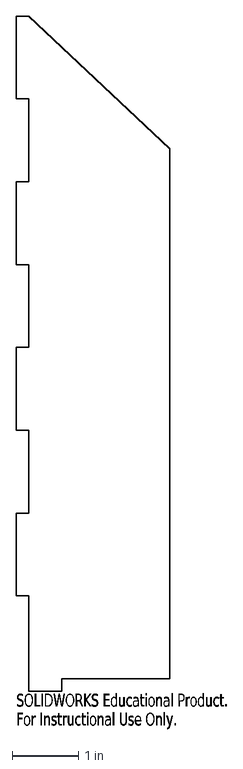
[picture p83: CAD file, 2022-02-18]
Laser Cutting/PPT_MiddleWall.DXF
SOLIDWORKS Educational Product.
For Instructional Use Only.
