donaldsonlab/PPT-Chamber/Main - 2 Chamber PPT/PPT_MiddleWall.SLDPRT

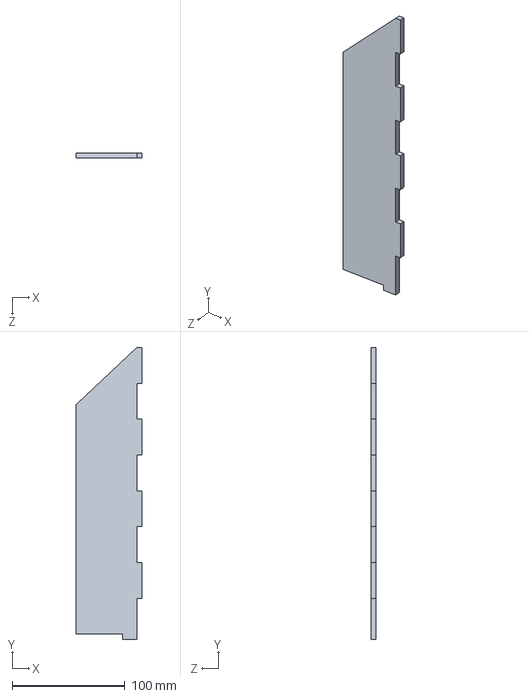
[picture p84: CAD file, 2022-02-18]
Main - 2 Chamber PPT/PPT_MiddleWall.SLDPRT
58.7 x 258.8 x 4.76 mm
